AchiraHansindu/Analog-Function-Generator/PCB Files/3D file/PHOTO-2023-12-06-23-20-29.jpg

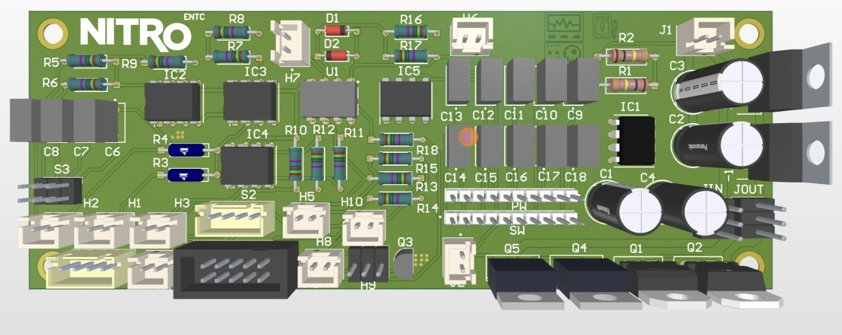
PCB Files/3D file/PHOTO-2023-12-06-23-20-29.jpg
